svenpetersen1965/PET-A-V-Interface/Case/Rev2/Label/Label_Barrel.png

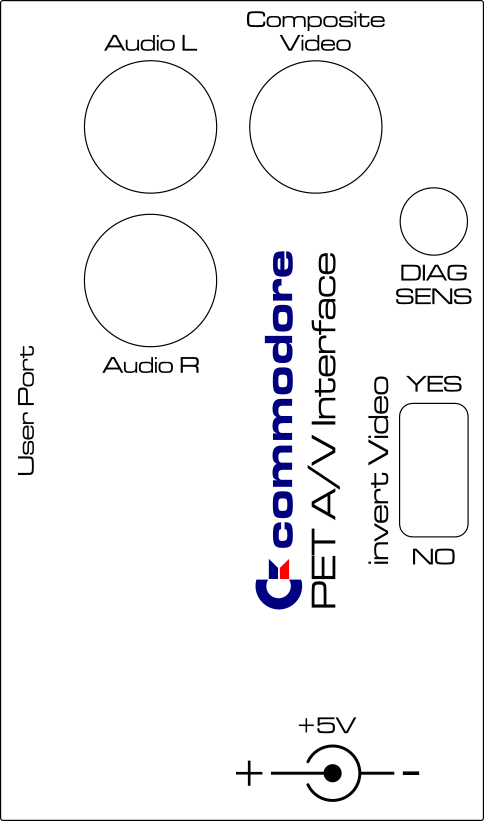
Case/Rev2/Label/Label_Barrel.png
