svenpetersen1965/PET-A-V-Interface/Case/Rev2/Label/Label_CPWr.jpg

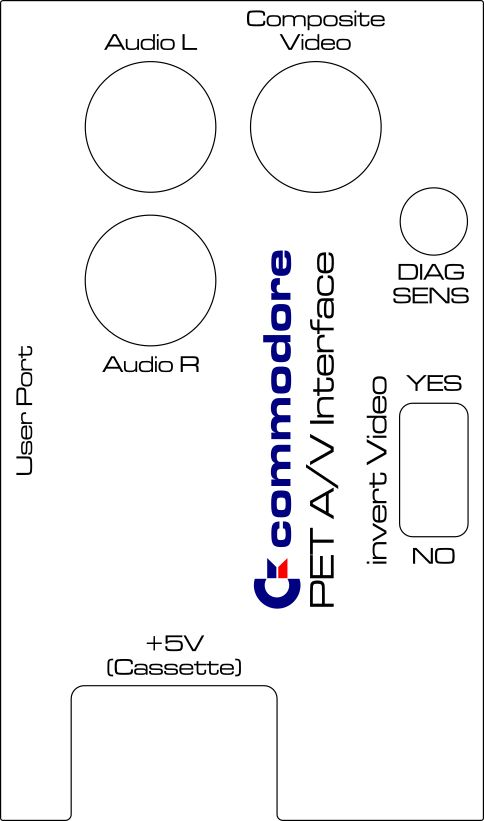
Case/Rev2/Label/Label_CPWr.jpg
