svenpetersen1965/PET-A-V-Interface/Case/Rev2/Label/Label_CPWr_flipped.png

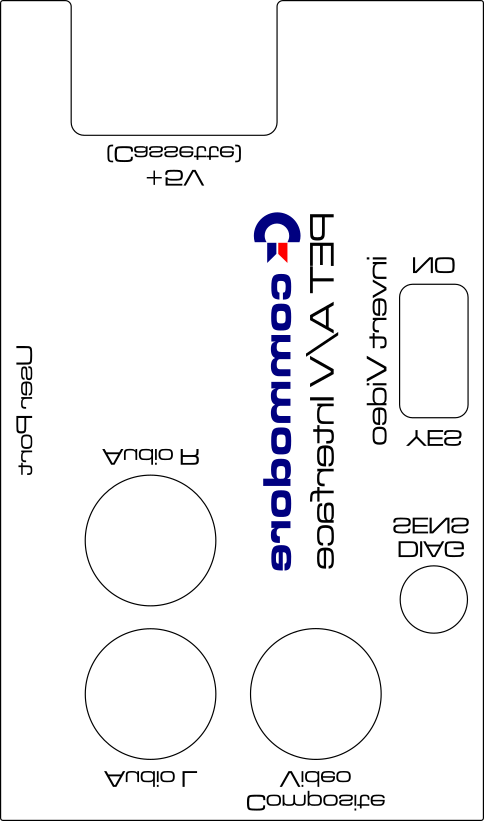
Case/Rev2/Label/Label_CPWr_flipped.png
